anatolij713/cas-powerbank/Img2.png

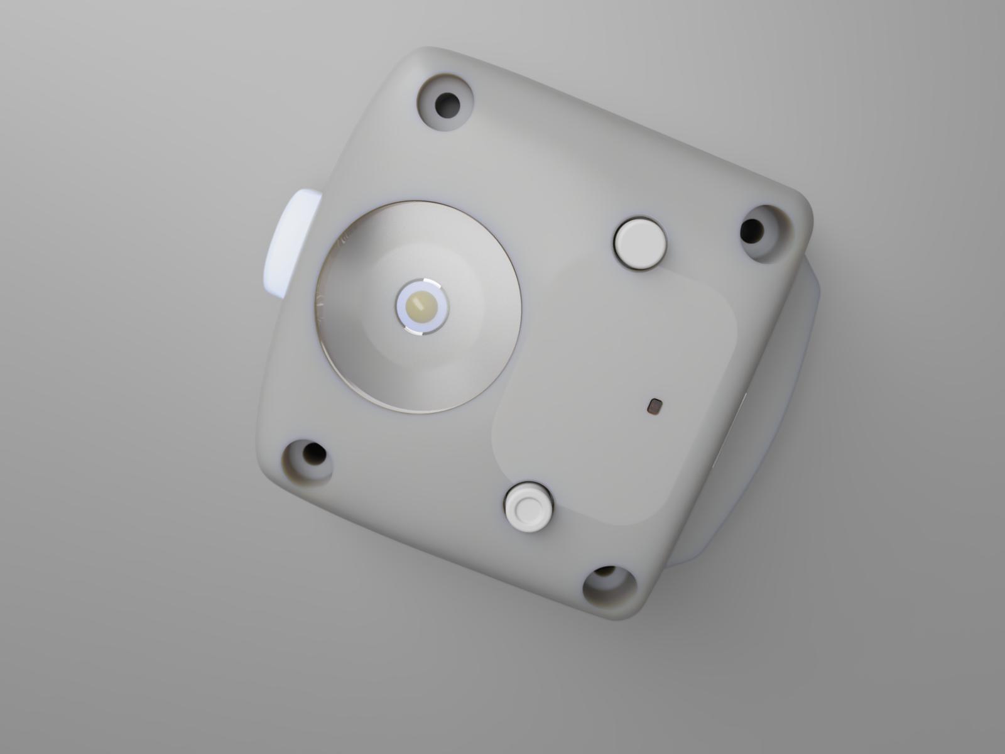
Img2.png
