anatolij713/cas-powerbank/Img3.png

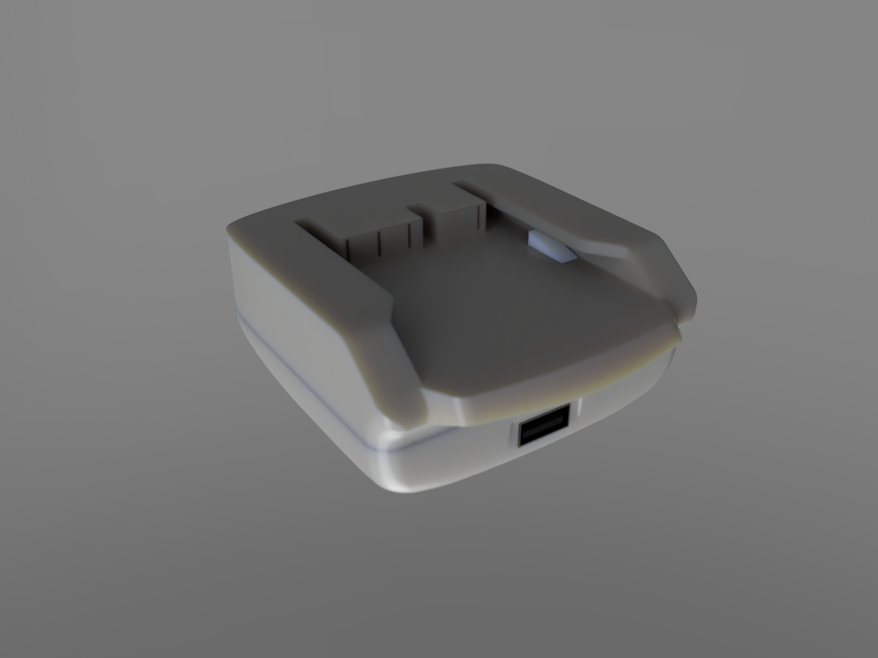
Img3.png
