anatolij713/cas-powerbank/Img4.png

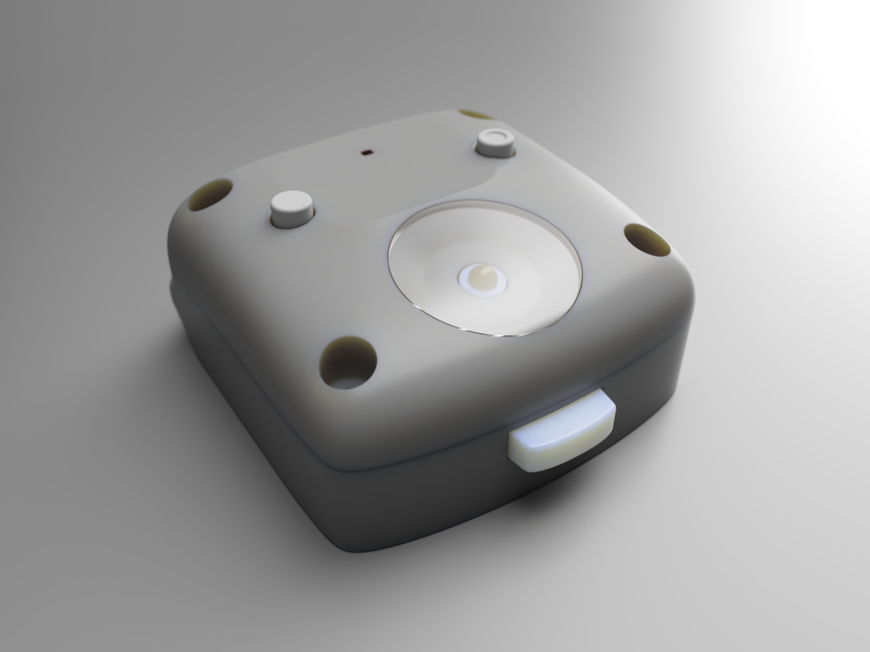
Img4.png
