anatolij713/cas-powerbank/Img5.png

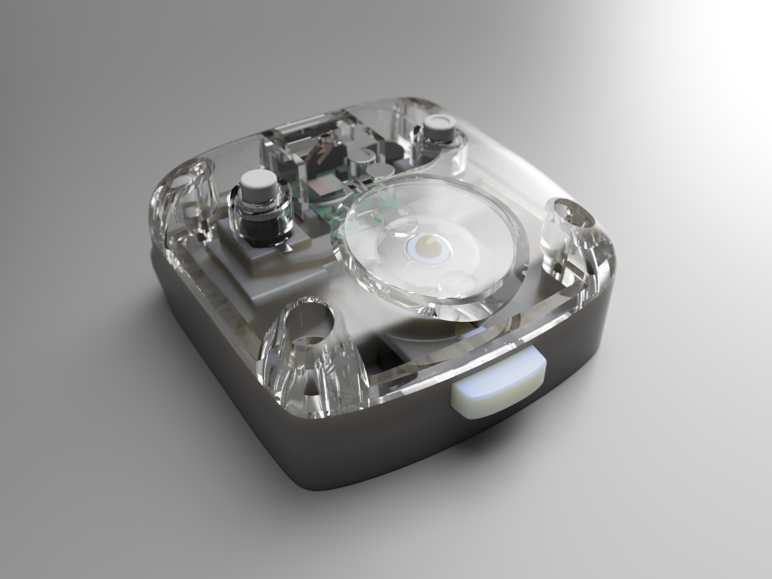
Img5.png
