anatolij713/cas-powerbank/Img6.png

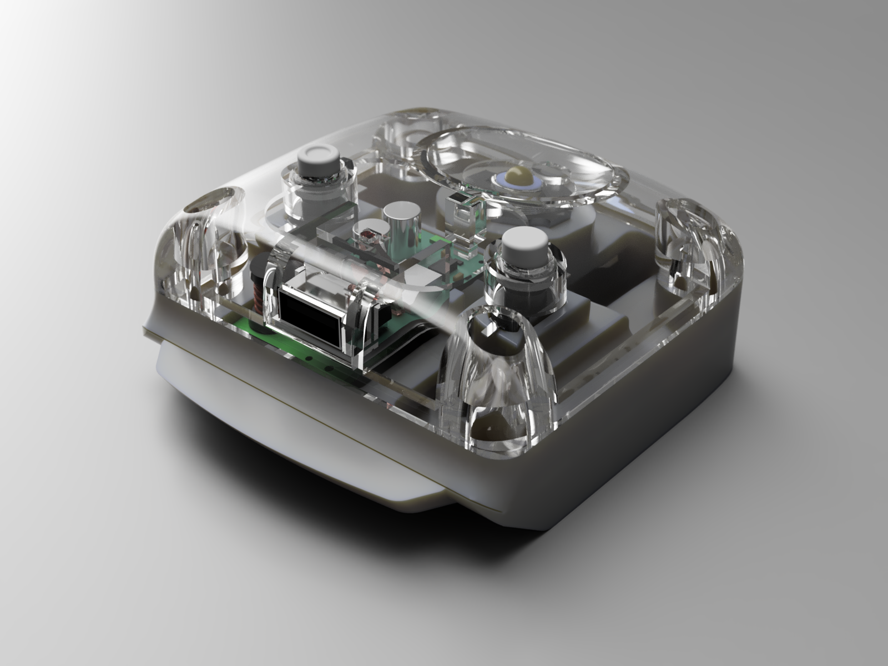
Img6.png
