anatolij713/cas-powerbank/Img7.png

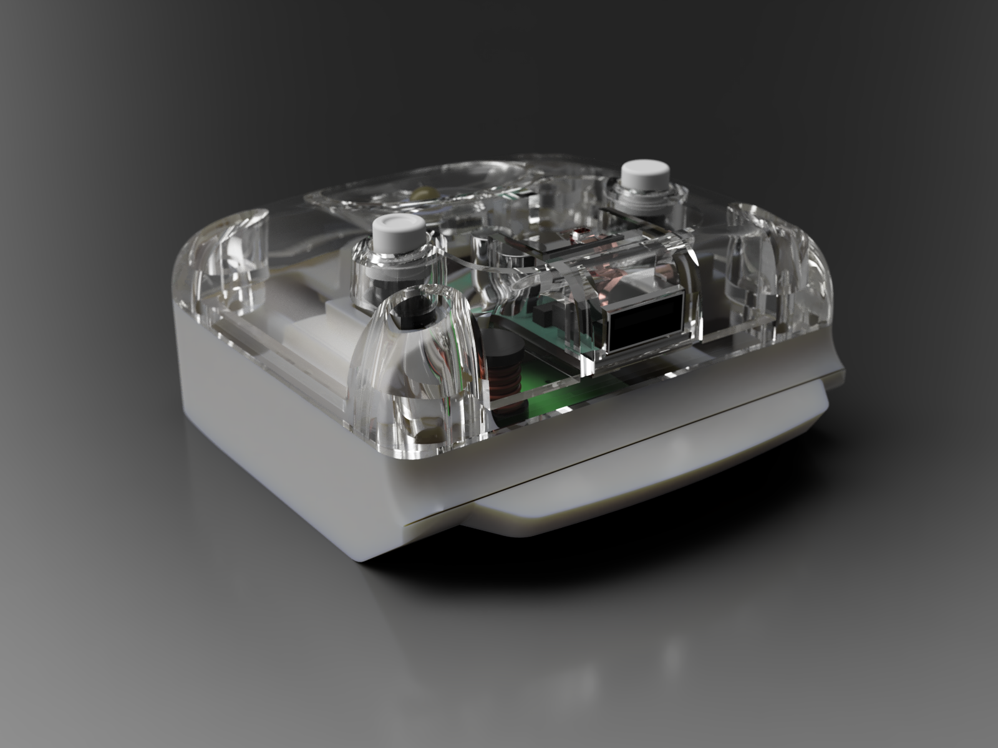
Img7.png
