anatolij713/cas-powerbank/Img8.png

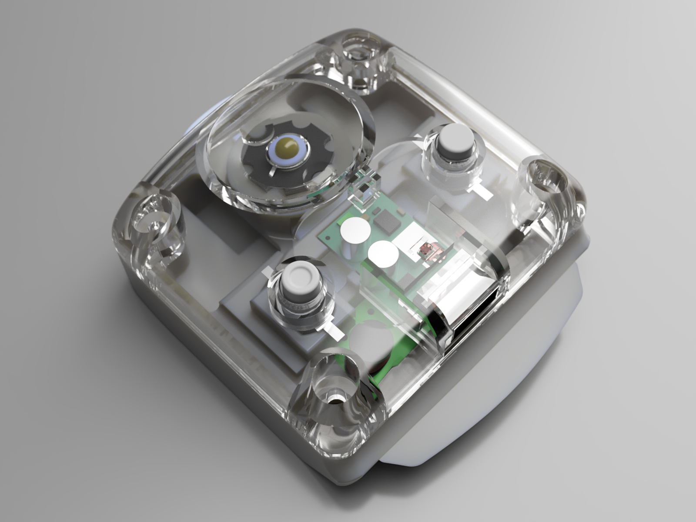
Img8.png
