anatolij713/cas-powerbank/Img9.png

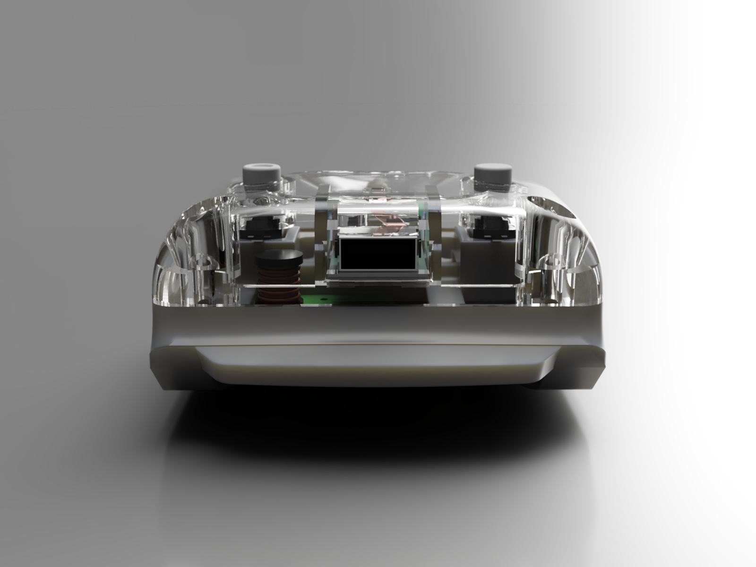
Img9.png
